Yamakaja/esp8266-ws2811/include/ws2812_i2c.h

//Copyright 2015 <>< Charles Lohr, See LICENSE file.
//WS2812 sender that abuses the I2S interface on the WS2812.

#ifndef _WS2812I2S_TEST
#define _WS2812I2S_TEST

//Stuff that should be for the header:

#include <c_types.h>

//Parameters for the I2S DMA behaviour
//#define I2SDMABUFCNT (2)			//Number of buffers in the I2S circular buffer
//#define I2SDMABUFLEN (32*2)		//Length of one buffer, in 32-bit words.

//NOTE: Blocksize MUST be divisible by 4.  Cannot exceed 4092
//Each LED takes up 12 block bytes in WS2812_FOUR_SAMPLE
//Or 9 block bytes in WS2812_THREE_SAMPLE
#define WS_BLOCKSIZE 4000

void ICACHE_FLASH_ATTR ws2812_init();
void ICACHE_FLASH_ATTR ws2812_push( uint8_t * buffer, uint16_t buffersize ); //Buffersize = Nr LEDs * 3

#endif
